rvl-system/rvl-firmware/boards/hub/_saved_Hub Board.sch

## KiCad design boards/hub/_saved_Hub Board.sch (2019-06-06)

Schematic: _saved_Hub Board.sch

Parts:
C1: 4.7uF; C_0805_HandSoldering
C2: 10uF; C_0805_HandSoldering
F0: Fuse; R_0805_HandSoldering
J1, J2, J3, J4: NeoPixel; Pin_Header_Angled_1x03_Pitch2.54mm
J5: Sensor; Pin_Header_Straight_1x03_Pitch2.00mm
L1: 2.2uH; R_0805_HandSoldering
P4: SERIAL; Pin_Header_Straight_1x03_Pitch2.00mm
R1: 1k; R_0805_HandSoldering
RP1, RP2: 10k; R_Array_Concave_4x2012.kicad_mod
SW1: Switch_SPDT_x2; CL-SA-12C4
SW2: Switch_DPST; KMR641NG
U0: 10118194
U1: LM3671; SOT-23-5_HandSoldering
U2: 74AUP1G14; SOT-23-5_HandSoldering
U3: ESP-12E; ESP-12E_SMD
U4: DIY-OLED-0.96
U5: SF303GJ26
U7: SN74LVC1T45; SOT-23-6_Handsoldering
