rvl-system/rvl-firmware/hub/src/input/input.cpp

/*
Copyright (c) 2017 Bryan Hughes <bryan@nebri.us>

This file is part of Raver Lights.

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
You should have received a copy of the GNU General Public License
along with Raver Lights.  If not, see <http://www.gnu.org/licenses/>.
*/

#include <Arduino.h>
#include "./input/input.h"
#include "./state.h"
#include "./codes.h"
#include "./config.h"

namespace Input {

enum ButtonChangeState {
  None = 0,
  Pressed = 1,
  Holding = 2
};

struct ButtonInfo {
  uint32 holdStartTime;
  byte state;
  byte gpio;
  byte on;
  byte off;
};

ButtonInfo nextButtonInfo = { 5, BUTTON_NEXT_OFF, BUTTON_NEXT, BUTTON_NEXT_ON, BUTTON_NEXT_OFF };
ButtonInfo upButtonInfo = { 5, BUTTON_UP_OFF, BUTTON_UP, BUTTON_UP_ON, BUTTON_UP_OFF };
ButtonInfo downButtonInfo = { 5, BUTTON_DOWN_OFF, BUTTON_DOWN, BUTTON_DOWN_ON, BUTTON_DOWN_OFF };

void init() {
  pinMode(nextButtonInfo.gpio, INPUT);
  pinMode(upButtonInfo.gpio, INPUT);
  pinMode(downButtonInfo.gpio, INPUT);
  Serial.println("Input initialized");
}

ButtonChangeState getButtonChangeState(ButtonInfo* buttonInfo) {
  ButtonChangeState returnValue = None;
  byte state = digitalRead(buttonInfo->gpio);
  if (state == buttonInfo->on) {
    uint32 now = millis();
    if (buttonInfo->holdStartTime == -1) {
      buttonInfo->holdStartTime = now;
    }
    uint32 holdTime = now - buttonInfo->holdStartTime;
    if (buttonInfo->state == buttonInfo->off) {
      if (holdTime > BUTTON_PRESS_ENGAGE_TIME) {
        buttonInfo->state = buttonInfo->on;
        returnValue = Pressed;
      }
    } else if (holdTime > BUTTON_HOLD_ENGAGE_TIME) {
      returnValue = Holding;
    }
  } else {
    buttonInfo->state = buttonInfo->off;
    buttonInfo->holdStartTime = -1;
  }
  return returnValue;
}

void loop() {
  switch (getButtonChangeState(&nextButtonInfo)) {
    case Pressed:
      State::nextControl();
      break;
    case Holding:
      // Do Nothing
      break;
    case None:
      // Do Nothing
      break;
  }

  switch (getButtonChangeState(&upButtonInfo)) {
    case Pressed:
      State::controlUp();
      break;
    case Holding:
      if (State::getSettings()->currentControl != Codes::Control::Preset) {
        State::controlUp();
      }
      break;
    case None:
      // Do Nothing
      break;
  }

  switch (getButtonChangeState(&downButtonInfo)) {
    case Pressed:
      State::controlDown();
      break;
    case Holding:
      if (State::getSettings()->currentControl != Codes::Control::Preset) {
        State::controlDown();
      }
      break;
    case None:
      // Do Nothing
      break;
  }
}

}  // namespace Input
