rvl-system/rvl-firmware/hub/src/messaging/protocols/giggle_pixel/giggle_pixel.cpp

/*
Copyright (c) 2018 Bryan Hughes <bryan@nebri.us>

This file is part of Raver Lights.

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
You should have received a copy of the GNU General Public License
along with Raver Lights.  If not, see <http://www.gnu.org/licenses/>.
*/

#include <Arduino.h>
#include "./messaging/protocols/giggle_pixel/giggle_pixel.h"
#include "./messaging/protocols/giggle_pixel/preset.h"
#include "./messaging/transport.h"
#include "../../../config.h"  // Why does this one single file require ".." but none of the others do?
#include "./codes.h"
#include "./state.h"

namespace GigglePixel {

const uint8 protocolVersion = 1;

void init() {
  Preset::init();
}

void loop() {
  Preset::loop();
}

struct GigglePixelHeader {
  uint8 protocolVersion;
  uint16 length;
  uint8 packetType;
  uint8 priority;
  uint16 sourceId;
};

void setClientId(uint16 id);
void broadcastHeader(uint8 packetType, uint8 priority, uint16 length);

bool readHeader(GigglePixelHeader& header) {
  header.protocolVersion = Transport::read8();
  if (header.protocolVersion != protocolVersion) {
    return false;
  }
  header.length = Transport::read16();
  header.packetType = Transport::read8();
  header.priority = Transport::read8();
  Transport::read8();  // Reserved
  header.sourceId = Transport::read16();
  return true;
}

void parsePacket() {
  Serial.println("Parsing GigglePixel packet");
  GigglePixelHeader headerDetails;
  if (!readHeader(headerDetails)) {
    Serial.println("Received unsupported GigglePixel protocol version packet");
    return;
  }

  switch (headerDetails.packetType) {
    case Codes::GigglePixelPacketTypes::Preset:
      Preset::parsePacket();
      break;
    default:
      Serial.print("Unsupported packet type received: ");
      Serial.println(headerDetails.packetType);
  }
}

void broadcastHeader(uint8 packetType, uint8 priority, uint16 length) {
  uint8* signature = const_cast<uint8*>(reinterpret_cast<const uint8*>("GLPX"));
  Transport::write(signature, sizeof(uint8) * 4);
  Transport::write8(protocolVersion);
  Transport::write16(length);
  Transport::write8(packetType);
  Transport::write8(priority);
  Transport::write8(0);  // reserved
  Transport::write16(State::getSettings()->id);
}

}  // namespace GigglePixel
