rvl-system/rvl-firmware/hub/src/messaging/messaging_client.cpp

/*
Copyright (c) 2016 Bryan Hughes <bryan@nebri.us>

This file is part of Raver Lights.

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
You should have received a copy of the GNU General Public License
along with Raver Lights.  If not, see <http://www.gnu.org/licenses/>.
*/

#include <Arduino.h>
#include <ESP8266WiFi.h>
#include <WiFiUdp.h>
#include "./messaging/messaging_client.h"
#include "../config.h"  // Why does this one single file require ".." but none of the others do?
#include "./codes.h"

namespace MessagingClient {

#define STATE_DISCONNECTED 0
#define STATE_CONNECTING 1
#define STATE_CONNECTED 2

byte state = STATE_DISCONNECTED;
uint32 nextTimeToPrintDot = 0;

void init() {
  Serial.println("Messaging Client initialized");
}

void loop() {
  // TODO(nebrius): re-enable and wire into state
  return;

  switch (state) {
    case STATE_DISCONNECTED:
      Serial.print("Connecting to ");
      Serial.print(WIFI_SSID);
      WiFi.begin(WIFI_SSID, WIFI_PASSPHRASE);
      state = STATE_CONNECTING;
      nextTimeToPrintDot = millis() + 500;
      // Fall through here instead of breaking
    case STATE_CONNECTING:
      if (WiFi.status() == WL_CONNECTED) {
        Serial.println();
        Serial.println("WiFi connected");
        Serial.println("IP address: ");
        Serial.println(WiFi.localIP());

        Serial.println("Starting UDP server");
        udp.begin(SERVER_PORT);
        state = STATE_CONNECTED;
      } else if (millis() >= nextTimeToPrintDot) {
        Serial.print(".");
        nextTimeToPrintDot = millis() + 500;
      }
      break;
    case STATE_CONNECTED:
      if (WiFi.status() != WL_CONNECTED) {
        Serial.println("Disconnected from WiFi, retrying");
        state = STATE_DISCONNECTED;
        break;
      }
      int packetSize = udp.parsePacket();
      if (packetSize == 0) {
        return;
      }
      Serial.print("Sync packet received");
      if (packetSize != 16) {
        Serial.println("Received incorrect packet size, resetting device...");
        ESP.reset();
      }

      uint32 commandTime;
      udp.read(static_cast<byte*>(static_cast<void*>(&commandTime)), 4);
      byte brightness = udp.read();
      byte preset = udp.read();
      byte presetValues[NUM_PRESET_VALUES];
      udp.read(presetValues, NUM_PRESET_VALUES);

      // TODO(nebrius): set state here
      // Lights::update(commandTime, brightness, (Codes::Preset::Preset)preset, presetValues);
      break;
  }
}

}  // namespace MessagingClient
