rvl-system/rvl-firmware/src/lights.cpp

/*
Copyright (c) 2016 Bryan Hughes <bryan@nebri.us>

This file is part of RVL Firmware.

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
You should have received a copy of the GNU General Public License
along with RVL Firmware.  If not, see <http://www.gnu.org/licenses/>.
*/

// ESP8266 specific stuff
#ifdef ESP8266
#define FASTLED_INTERRUPT_RETRY_COUNT 0 // Helps keep LEDs from flickering
#define FASTLED_ESP8266_RAW_PIN_ORDER
#endif

#include "./lights.hpp"
#include "./config.hpp"
#include <Arduino.h>
#include <FastLED.h>
#include <rvl.hpp>
#include <rvl/config.hpp>
#include <variant>

namespace Lights {

CRGB leds[LED_NUM_PIXELS];
// The outgoing scene of a dissolve. Here rather than on the loop task's stack
CRGB fadeFrom[LED_NUM_PIXELS];
bool blanked = false;

void init() {
  // Segment ends are inclusive and index leds directly, so an end past the last
  // pixel writes into whatever global the linker placed after the array
  for (auto& segment : segments) {
    if (segment.end >= LED_NUM_PIXELS) {
      rvl::error("Segment end %d is past the last pixel %d, clamping",
          segment.end, LED_NUM_PIXELS - 1);
      segment.end = LED_NUM_PIXELS - 1;
    }
  }
  FastLED.addLeds<WS2812B, LED_DATA_PIN, LED_COLOR_MODE>(leds, LED_NUM_PIXELS);
  rvl::info("Lights initialized");
}

uint8_t calculatePixelValue(
    const RVLColorComponent& component, uint32_t t, uint8_t x) {
  return sin8(component.w_t * t / 100 + component.w_x * x + component.phi) *
      component.a / 255 +
      component.b;
}

void renderParametric(
    const RVLParametricSettings& settings, uint32_t animationClock, CRGB* out) {
  uint32_t t =
      animationClock % (settings.timePeriod * 100) * 255 / settings.timePeriod;
  for (const auto& segment : segments) {
    for (uint16_t i = segment.start; i <= segment.end; i++) {
      uint16_t normalizedIndex = 0;
      if (segment.reverse) {
        normalizedIndex = (segment.end - i) + segment.offset;
      } else {
        normalizedIndex = (i - segment.start) + segment.offset;
      }
      uint8_t x = 255 * (normalizedIndex % settings.distancePeriod) /
          settings.distancePeriod;

      CHSV layerHSV[NUM_LAYERS];
      CRGB layerRGB[NUM_LAYERS];
      uint8_t alphaValues[NUM_LAYERS];

      for (uint8_t j = 0; j < NUM_LAYERS; j++) {
        layerHSV[j].h = calculatePixelValue(settings.layers[j].h, t, x);
        layerHSV[j].s = calculatePixelValue(settings.layers[j].s, t, x);
        layerHSV[j].v = calculatePixelValue(settings.layers[j].v, t, x);
        alphaValues[j] = calculatePixelValue(settings.layers[j].a, t, x);
        hsv2rgb_spectrum(layerHSV[j], layerRGB[j]);
      }
      out[i] = layerRGB[NUM_LAYERS - 1];
      for (int8_t j = NUM_LAYERS - 2; j >= 0; j--) {
        out[i] = blend(out[i], layerRGB[j], alphaValues[j]);
      }
    }
  }
}

// At the frame's time rather than a live clock read, so both renders of a
// dissolve, and every board's render of a frame, see the same instant
void renderScene(const RVLScene& scene, uint32_t frame, CRGB* out) {
  const auto* settings = std::get_if<RVLParametricSettings>(&scene.content);
  if (settings != nullptr) {
    renderParametric(*settings, frame * FRAME_PERIOD, out);
  } else {
    fill_solid(out, LED_NUM_PIXELS, CRGB::Black);
  }
}

void loop() {
  rvl::RenderPlan plan = rvl::getRenderPlan();
  // Blanks rather than showing the local preset or another channel's animation
  // before this node knows what the fleet is showing, and once an off scene has
  // finished dissolving in
  bool blank = rvl::getRenderState() == rvl::RenderState::Unknown ||
      (std::holds_alternative<RVLOff>(plan.current.content) && !plan.fading);
  if (blank) {
    if (!blanked) {
      // Clears leds[] too, so nothing that shows it later can bring back the
      // frame from before the strip went dark
      FastLED.clear(true);
      blanked = true;
    }
    return;
  }
  blanked = false;

  renderScene(plan.current, plan.frame, leds);
  if (plan.fading) {
    renderScene(plan.previous, plan.frame, fadeFrom);
    for (uint16_t i = 0; i < LED_NUM_PIXELS; i++) {
      leds[i] = blend(fadeFrom[i], leds[i], plan.amount);
    }
  }
  FastLED.setBrightness(rvl::getBrightness());
  FastLED.show();
}

} // namespace Lights
