rvl-system/rvl-firmware/src/ui/control.hpp

/*
Copyright (c) Bryan Hughes <bryan@nebri.us>

This file is part of RVL Firmware.

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
You should have received a copy of the GNU General Public License
along with RVL Firmware.  If not, see <http://www.gnu.org/licenses/>.
*/

#ifndef UI_CONTROL_H_
#define UI_CONTROL_H_

#include <Arduino.h>
#include <utility>
#include <vector>

namespace Control {

enum class ControlType : uint8_t { Range, List, Label };

class Control {
public:
  const char* label;
  ControlType type;
  void (*updateValue)(uint8_t newValue);

  Control(const char* controlLabel, ControlType controlType,
      void (*updateValueCallback)(uint8_t newValue))
      : label(controlLabel), type(controlType),
        updateValue(updateValueCallback) {}

  virtual void increaseValue() {}
  virtual void decreaseValue() {}
};

class ListControl : public Control {
public:
  std::vector<const char*> values;
  uint8_t selectedValueIndex;

  ListControl(const char* listLabel, std::vector<const char*> listValues,
      uint8_t defaultValueIndex, void (*updateValueCallback)(uint8_t newValue))
      : Control(listLabel, ControlType::List, updateValueCallback),
        values(std::move(listValues)), selectedValueIndex(defaultValueIndex) {}

  void increaseValue() override {
    if (this->selectedValueIndex == this->values.size() - 1) {
      this->selectedValueIndex = 0;
    } else {
      this->selectedValueIndex++;
    }
    this->updateValue(this->selectedValueIndex);
  }

  void decreaseValue() override {
    if (this->selectedValueIndex == 0) {
      this->selectedValueIndex = this->values.size() - 1;
    } else {
      this->selectedValueIndex--;
    }
    this->updateValue(this->selectedValueIndex);
  }
};

class RangeControl : public Control {
public:
  uint8_t value;
  uint8_t min;
  uint8_t max;
  uint8_t (*getValue)();

  RangeControl(const char* rangeLabel, uint8_t rangeMin, uint8_t rangeMax,
      uint8_t defaultValue, void (*updateValueCallback)(uint8_t newValue),
      uint8_t (*getValueMethod)())
      : Control(rangeLabel, ControlType::Range, updateValueCallback),
        value(defaultValue), min(rangeMin), max(rangeMax),
        getValue(getValueMethod) {}

  void increaseValue() override {
    if (this->value < this->max) {
      this->value++;
      this->updateValue(this->value);
    }
  }

  void decreaseValue() override {
    if (this->value > this->min) {
      this->value--;
      this->updateValue(this->value);
    }
  }
};

class LabelControl : public Control {
public:
  void (*getValue)(char* buffer, size_t size);

  LabelControl(
      const char* labelLabel, void (*getValueMethod)(char* buffer, size_t size))
      : Control(labelLabel, ControlType::Label, nullptr),
        getValue(getValueMethod) {}
};

} // namespace Control

#endif // UI_CONTROL_H_
